papapumpkins/disa-myo-bionic-arm/20160616_183405.jpg

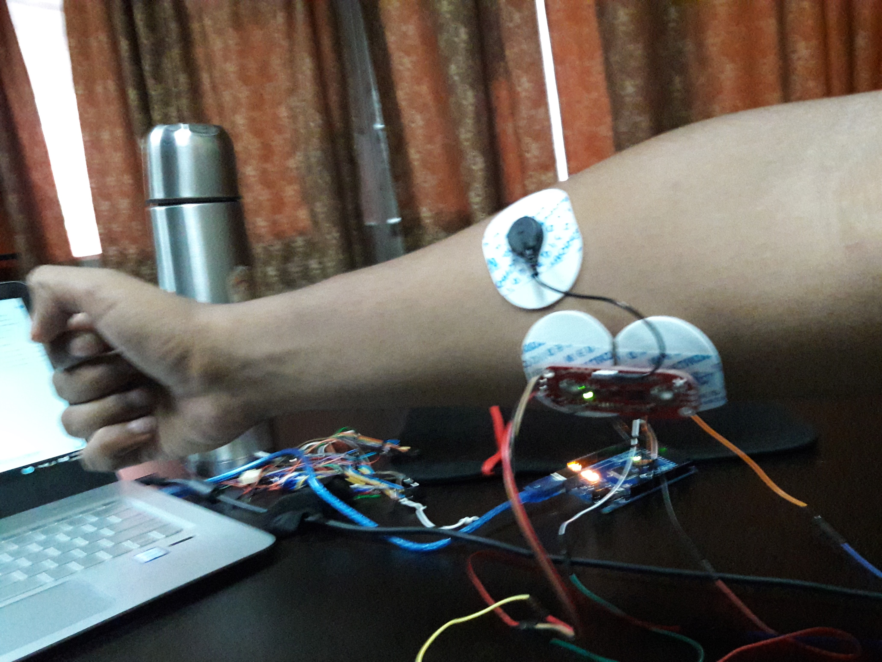
20160616_183405.jpg
