papapumpkins/disa-myo-bionic-arm/Servo CAD/futaba-servo/Renderings/Servo20111002-25129-4bc1xx.JPG

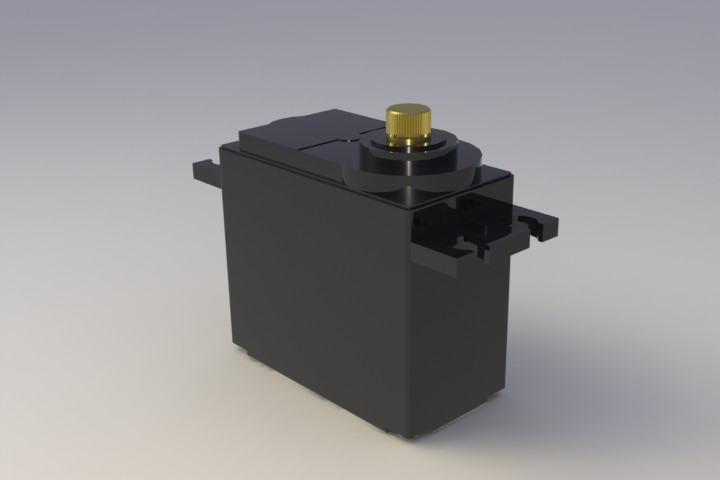
Servo CAD/futaba-servo/Renderings/Servo20111002-25129-4bc1xx.JPG
