papapumpkins/disa-myo-bionic-arm/Servo CAD/micro-servo-9g-1.snapshot.2/Renderings/MicroServo9g.png

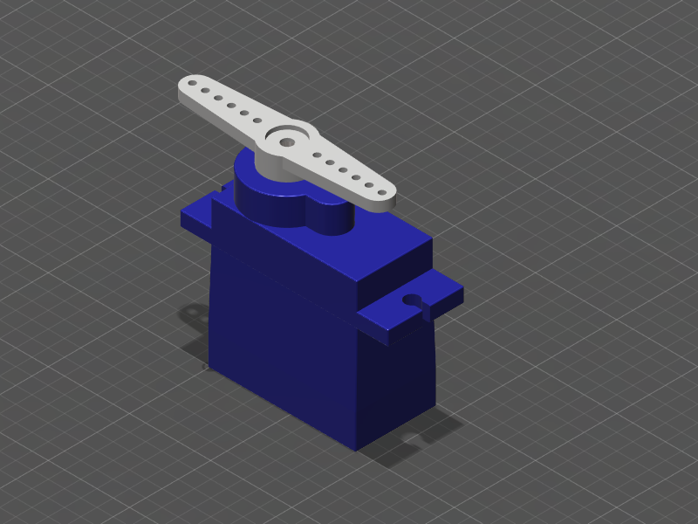
Servo CAD/micro-servo-9g-1.snapshot.2/Renderings/MicroServo9g.png
