papapumpkins/disa-myo-bionic-arm/Digits_Fingers_Base_20161126/Ring/Ring STL/Ring_Finger_assembly_1_Shaft_Piston_4.stl

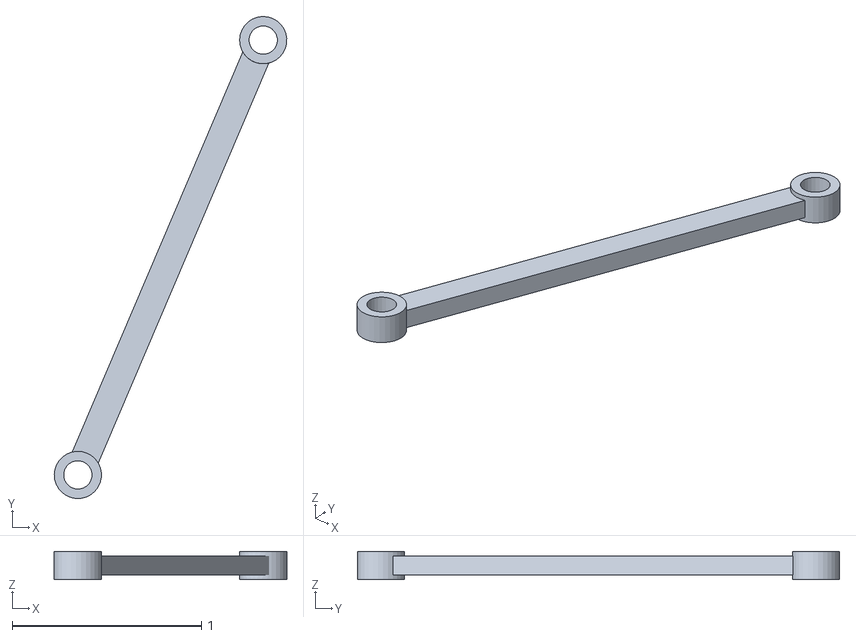
[picture p31: CAD file, 2018-10-29]
Digits_Fingers_Base_20161126/Ring/Ring STL/Ring_Finger_assembly_1_Shaft_Piston_4.stl
1.23 x 2.55 x 0.15
