papapumpkins/disa-myo-bionic-arm/Digits_Fingers_Base_20161126/ZIP STL 1/Pinky STL/Pinky_Assembly_01_Shaft_Piston_3.stl

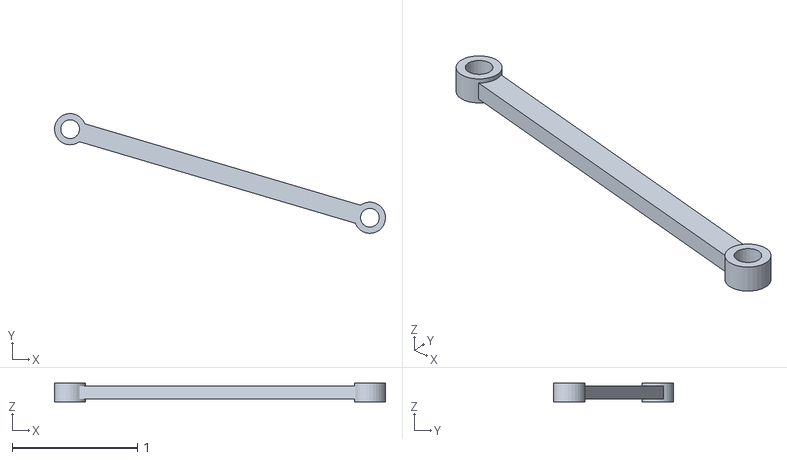
[picture p32: CAD file, 2018-10-29]
Digits_Fingers_Base_20161126/ZIP STL 1/Pinky STL/Pinky_Assembly_01_Shaft_Piston_3.stl
2.65 x 0.958 x 0.15
