papapumpkins/disa-myo-bionic-arm/Digits_Fingers_Base_20161126/ZIP STL 1/Thumb STL/Thumb_assembly_1.stl

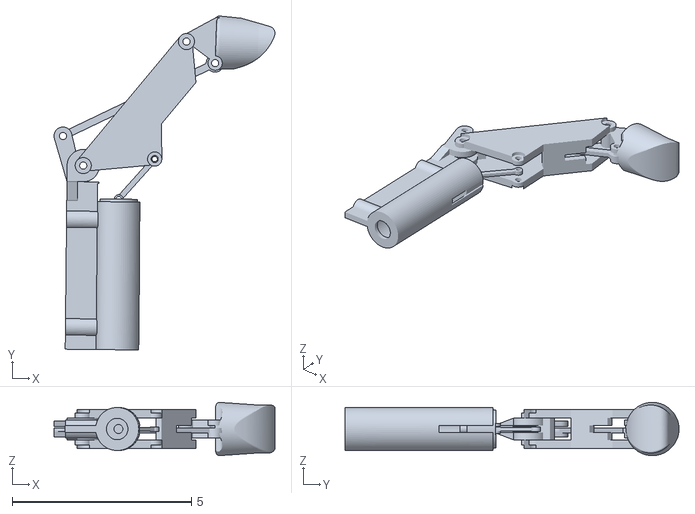
[picture p33: CAD file, 2018-10-29]
Digits_Fingers_Base_20161126/ZIP STL 1/Thumb STL/Thumb_assembly_1.stl
6.16 x 9.31 x 1.49
