papapumpkins/disa-myo-bionic-arm/Digits_Fingers_Base_20161126/ZIP STL 2/Index STL/Index_Finger_assembly_1_Shaft_Piston_2.stl

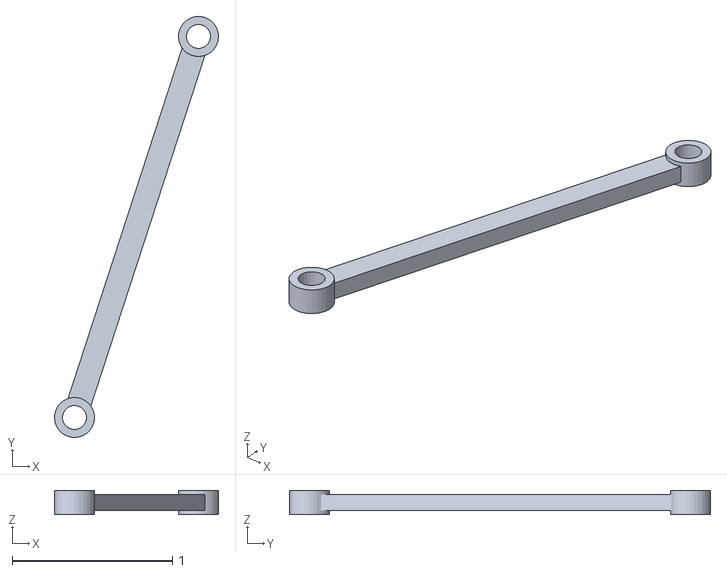
[picture p34: CAD file, 2018-10-29]
Digits_Fingers_Base_20161126/ZIP STL 2/Index STL/Index_Finger_assembly_1_Shaft_Piston_2.stl
1.02 x 2.63 x 0.15
