papapumpkins/disa-myo-bionic-arm/Digits_Fingers_Base_20161126/ZIP STL 2/Pinky STL/Pinky_ASSEMBLY_DONT_PRINT.stl

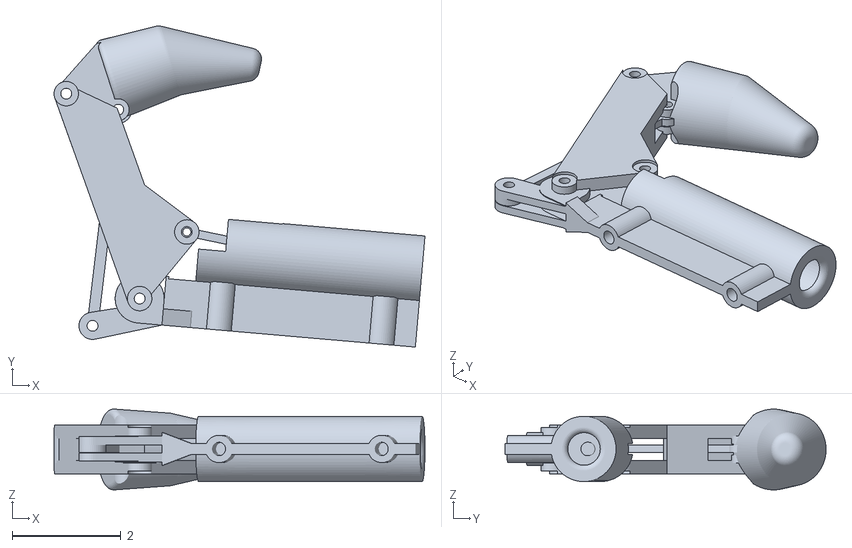
[picture p35: CAD file, 2018-10-29]
Digits_Fingers_Base_20161126/ZIP STL 2/Pinky STL/Pinky_ASSEMBLY_DONT_PRINT.stl
6.82 x 5.90 x 1.49
