papapumpkins/disa-myo-bionic-arm/Digits_Fingers_Base_20161029/Index+Middle/STL/Index_Finger_assembly_1_Base_Cylinder_11mm_5.stl

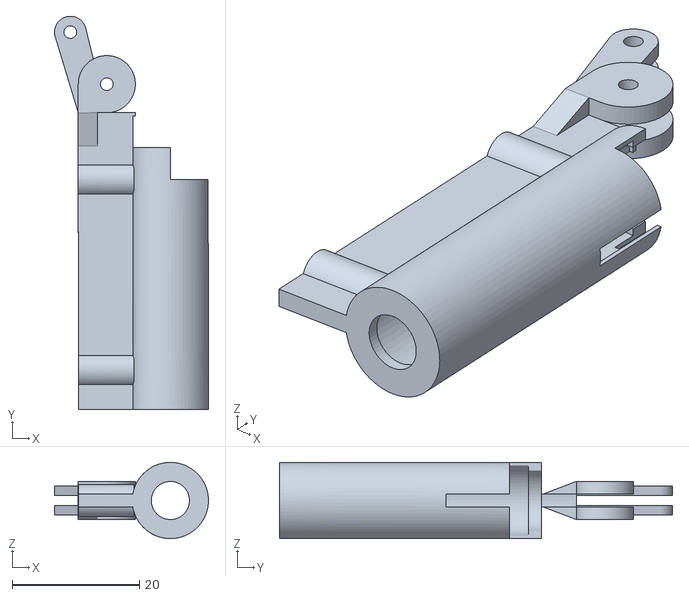
[picture p36: CAD file, 2018-10-29]
Digits_Fingers_Base_20161029/Index+Middle/STL/Index_Finger_assembly_1_Base_Cylinder_11mm_5.stl
24.2 x 61.9 x 12.0
