papapumpkins/disa-myo-bionic-arm/Digits_Fingers_Base_20161029/Pinky/Pinky_STL/Pinky_Assembly_01_Pinky_Upper_main_2_6.stl

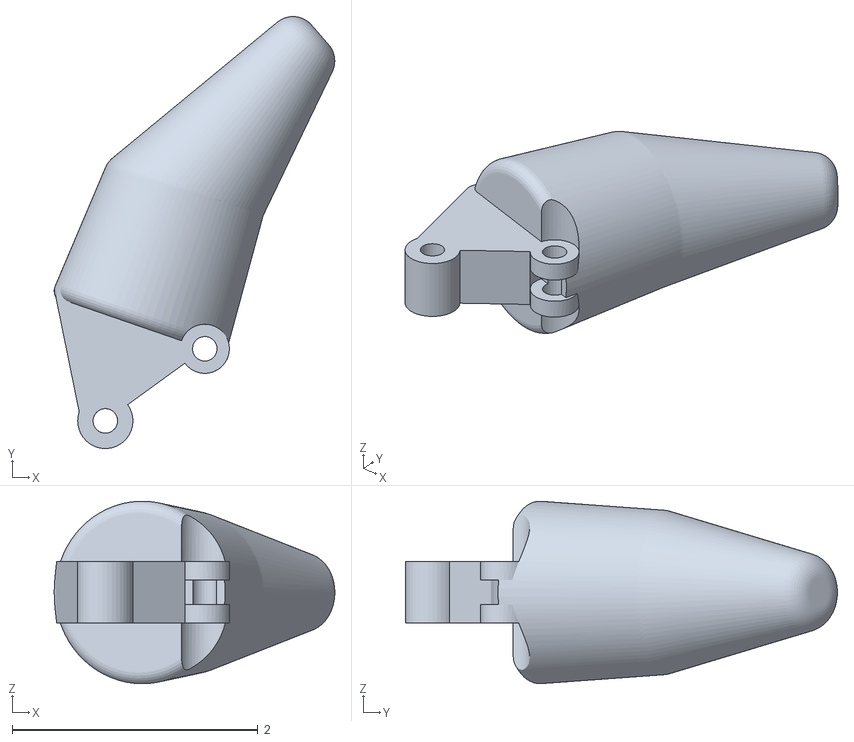
[picture p37: CAD file, 2018-10-29]
Digits_Fingers_Base_20161029/Pinky/Pinky_STL/Pinky_Assembly_01_Pinky_Upper_main_2_6.stl
2.28 x 3.52 x 1.49
