papapumpkins/disa-myo-bionic-arm/Digits_Fingers_Base_20161029/Ring/Ring STL/Ring_Finger_assembly_1_Ring_Upper_main_1_3.stl

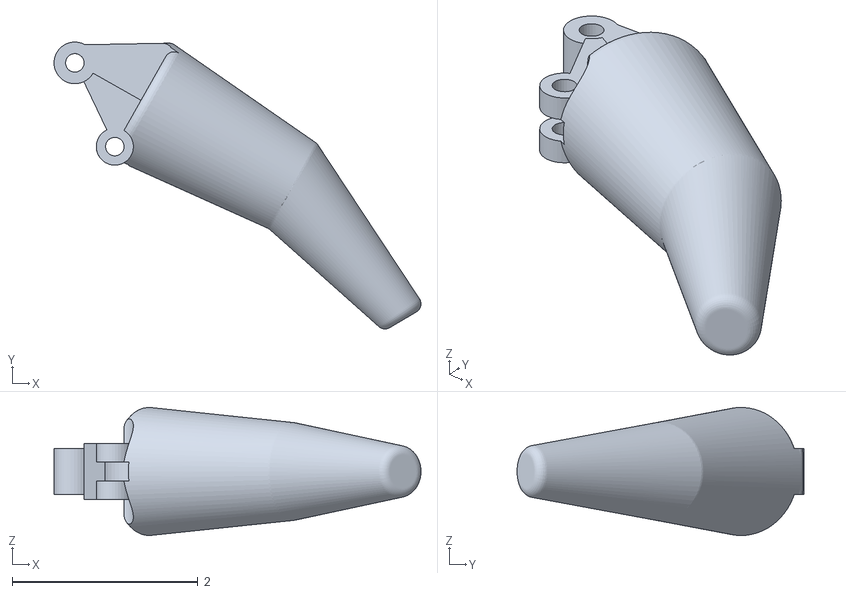
[picture p38: CAD file, 2018-10-29]
Digits_Fingers_Base_20161029/Ring/Ring STL/Ring_Finger_assembly_1_Ring_Upper_main_1_3.stl
3.96 x 3.09 x 1.38
