papapumpkins/disa-myo-bionic-arm/Digits_Fingers_Base_20161029/ZIP STL 1/Index STL/Index_Finger_assembly_1_Shaft_Piston_2.stl

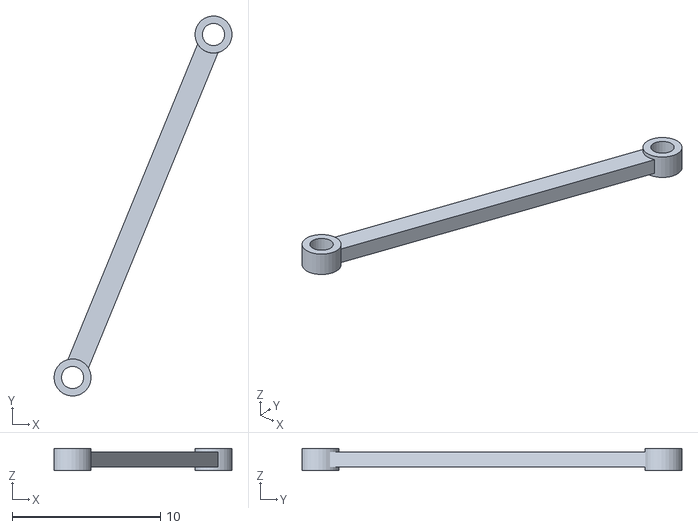
[picture p39: CAD file, 2018-10-29]
Digits_Fingers_Base_20161029/ZIP STL 1/Index STL/Index_Finger_assembly_1_Shaft_Piston_2.stl
12.0 x 25.6 x 1.50
