papapumpkins/disa-myo-bionic-arm/Digits_Fingers_Base_20161029/ZIP STL 1/Pinky STL/Pinky_Assembly_01.stl

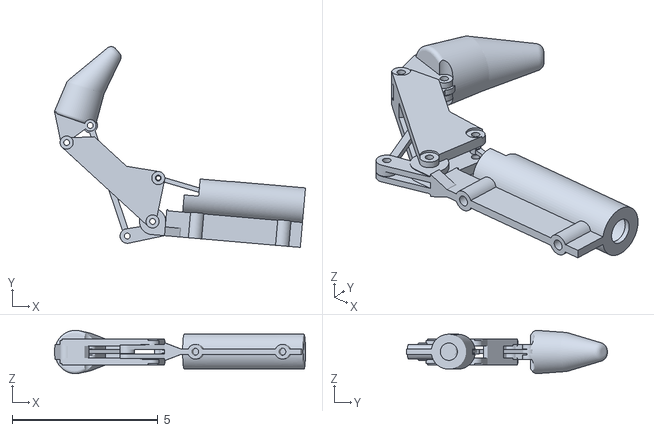
[picture p40: CAD file, 2018-10-29]
Digits_Fingers_Base_20161029/ZIP STL 1/Pinky STL/Pinky_Assembly_01.stl
8.61 x 6.89 x 1.49
