papapumpkins/disa-myo-bionic-arm/Digits_Fingers_Base_20161029/ZIP STL 2/Pinky STL/Pinky_Assembly_01_Base_Cylinder_Pinky_11mm_4.stl

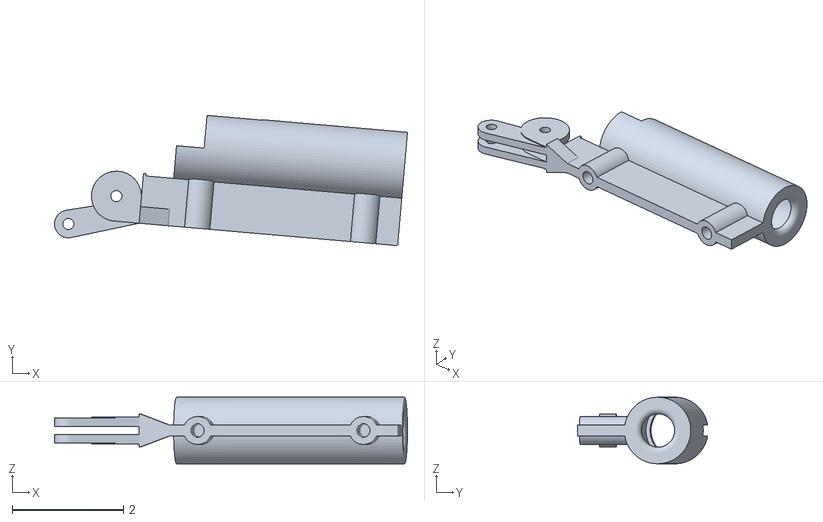
[picture p41: CAD file, 2018-10-29]
Digits_Fingers_Base_20161029/ZIP STL 2/Pinky STL/Pinky_Assembly_01_Base_Cylinder_Pinky_11mm_4.stl
6.36 x 2.35 x 1.20
