papapumpkins/disa-myo-bionic-arm/Digits_Fingers_Base_20161029/ZIP STL 2/Thumb STL/Thumb_assembly_1_Thumb_Restrain_Pin_1_3.stl

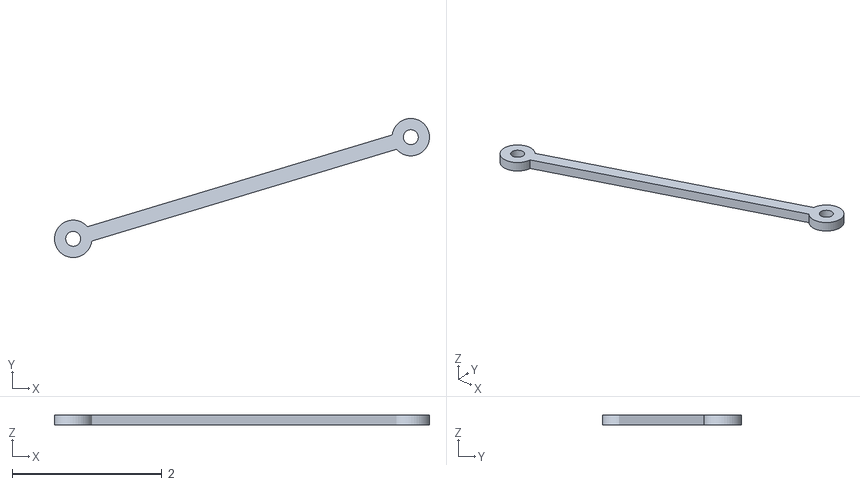
[picture p42: CAD file, 2018-10-29]
Digits_Fingers_Base_20161029/ZIP STL 2/Thumb STL/Thumb_assembly_1_Thumb_Restrain_Pin_1_3.stl
5.00 x 1.86 x 0.14
