papapumpkins/disa-myo-bionic-arm/Digits_Fingers_Base_20161126/Pinky/Pinky_STL/Pinky_Assembly_01_Pinky_Lower_main_1_5.stl

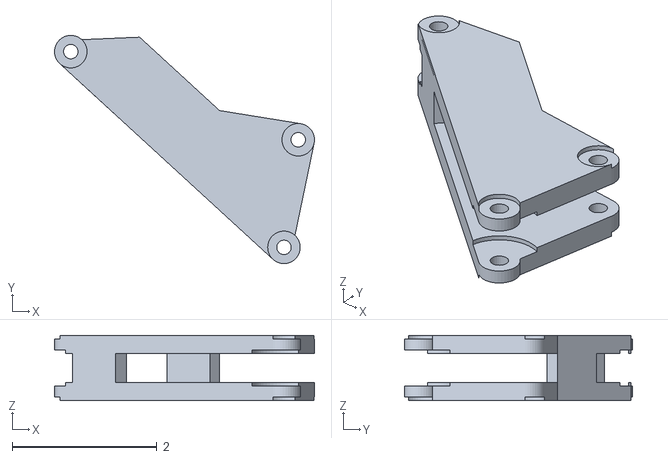
[picture p43: CAD file, 2018-10-29]
Digits_Fingers_Base_20161126/Pinky/Pinky_STL/Pinky_Assembly_01_Pinky_Lower_main_1_5.stl
3.59 x 3.15 x 0.9
