papapumpkins/disa-myo-bionic-arm/Digits_Fingers_Base_20161126/Thumb/Thumb_STL/Thumb_assembly_1_Thumb_Lower_main_1_1.stl

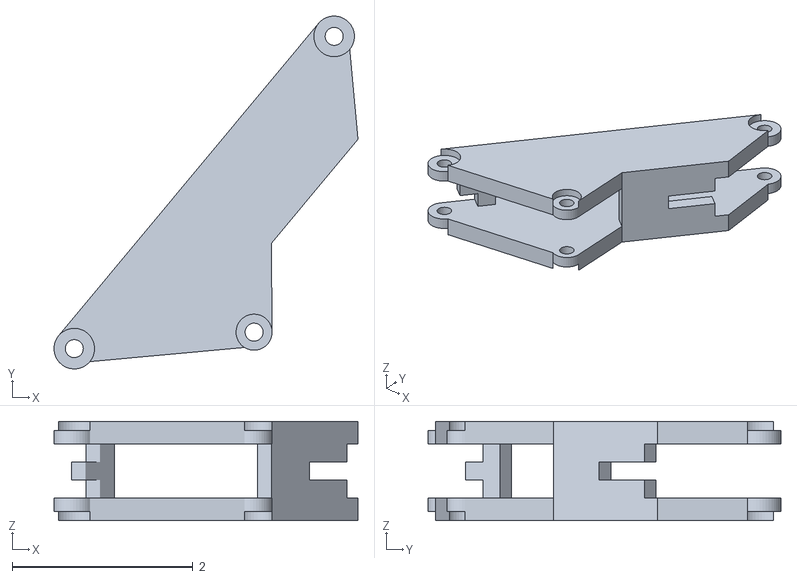
[picture p44: CAD file, 2018-10-29]
Digits_Fingers_Base_20161126/Thumb/Thumb_STL/Thumb_assembly_1_Thumb_Lower_main_1_1.stl
3.37 x 3.91 x 1.10
