papapumpkins/disa-myo-bionic-arm/Digits_Fingers_Base_20161126/ZIP STL 1/Index STL/Index_Finger_assembly_1_Index_Upper_main_1_4.stl

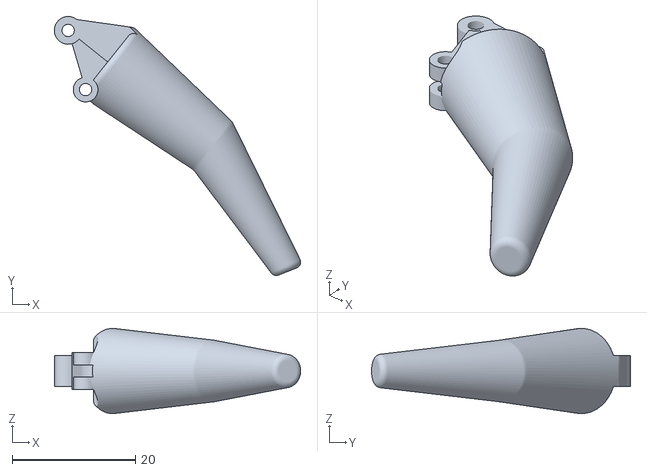
[picture p45: CAD file, 2018-10-29]
Digits_Fingers_Base_20161126/ZIP STL 1/Index STL/Index_Finger_assembly_1_Index_Upper_main_1_4.stl
39.9 x 42.0 x 13.8
