papapumpkins/disa-myo-bionic-arm/Digits_Fingers_Base_20161126/ZIP STL 1/Middle STL (Same as Index)/Index_Finger_assembly_1_Cylinder_10.5mm_6.stl

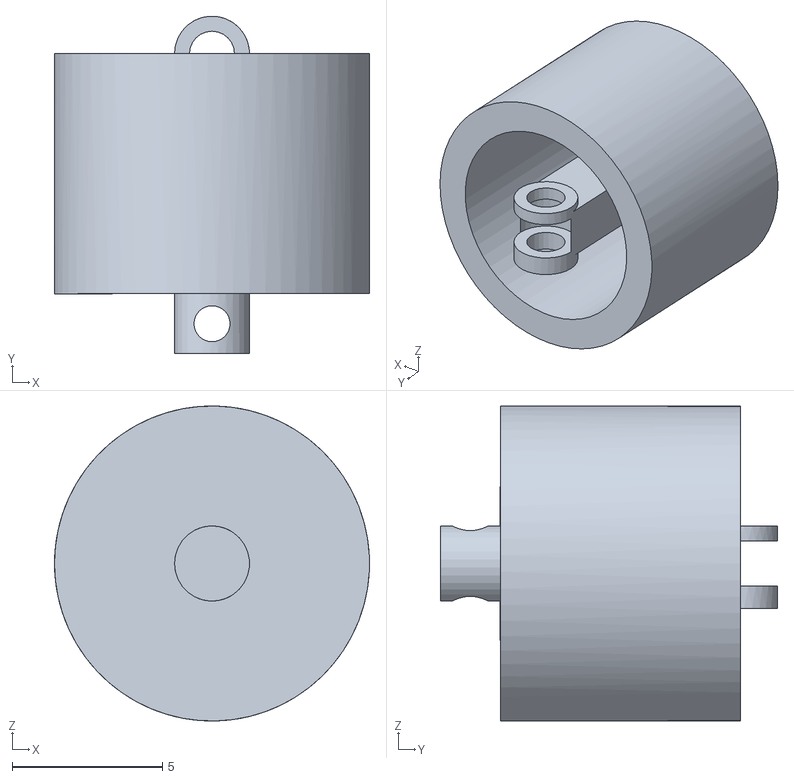
[picture p46: CAD file, 2018-10-29]
Digits_Fingers_Base_20161126/ZIP STL 1/Middle STL (Same as Index)/Index_Finger_assembly_1_Cylinder_10.5mm_6.stl
10.5 x 11.2 x 10.5
