papapumpkins/disa-myo-bionic-arm/Digits_Fingers_Base_20161126/ZIP STL 1/Ring STL/Ring_Finger_assembly_1_Restrain_Pin_1_2.stl

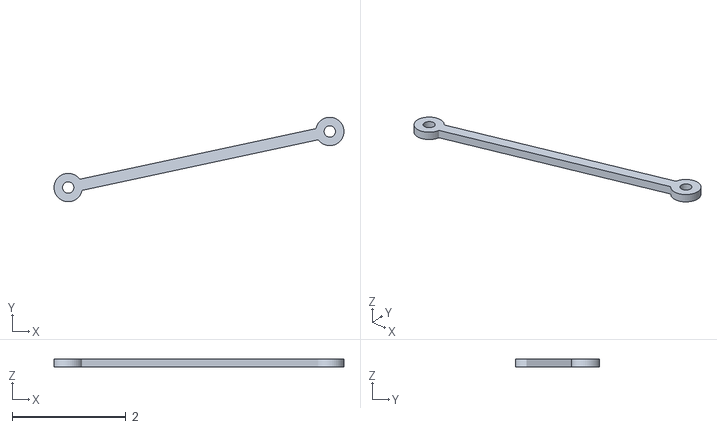
[picture p47: CAD file, 2018-10-29]
Digits_Fingers_Base_20161126/ZIP STL 1/Ring STL/Ring_Finger_assembly_1_Restrain_Pin_1_2.stl
5.10 x 1.49 x 0.14
