papapumpkins/disa-myo-bionic-arm/Digits_Fingers_Base_20161126/ZIP STL 2/Ring STL/Ring_Finger_assembly_1_Finger_Lower_main_1_1.stl

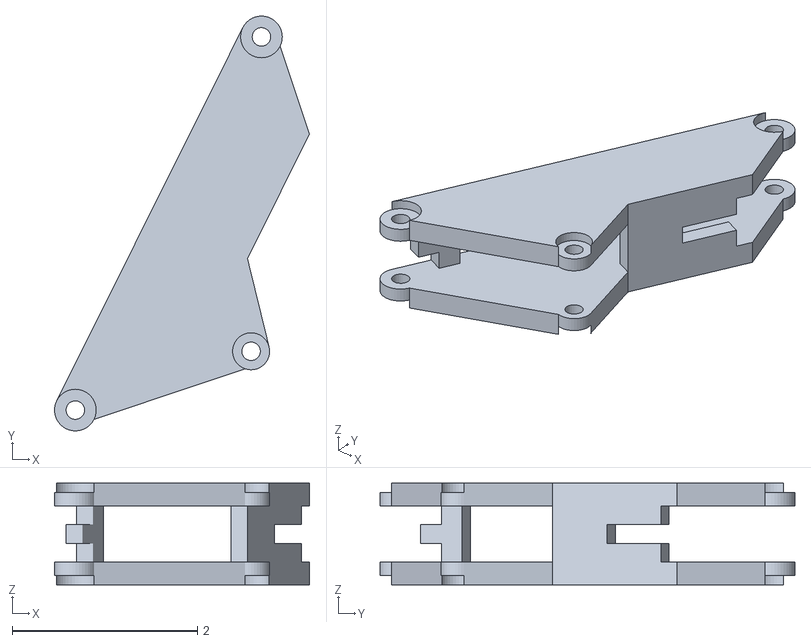
[picture p48: CAD file, 2018-10-29]
Digits_Fingers_Base_20161126/ZIP STL 2/Ring STL/Ring_Finger_assembly_1_Finger_Lower_main_1_1.stl
2.75 x 4.48 x 1.10
