papapumpkins/disa-myo-bionic-arm/Digits_Fingers_Base_20161029/Thumb/Thumb_STL/Thumb_assembly_1_ThumbNew_Base_Cylinder_11mm_4.stl

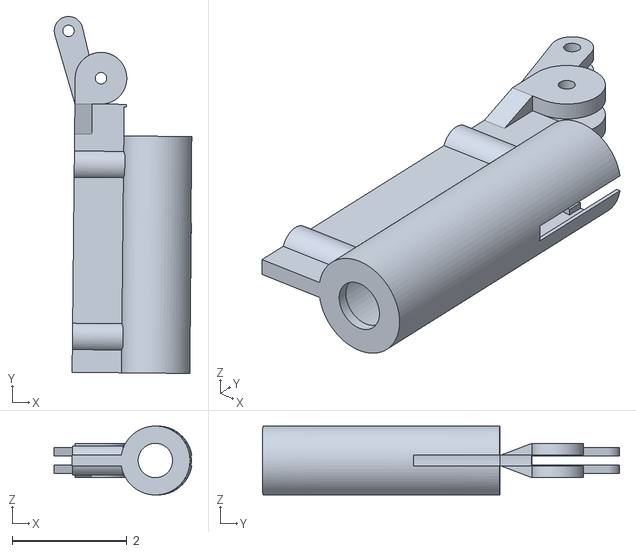
[picture p49: CAD file, 2018-10-29]
Digits_Fingers_Base_20161029/Thumb/Thumb_STL/Thumb_assembly_1_ThumbNew_Base_Cylinder_11mm_4.stl
2.40 x 6.22 x 1.20
