papapumpkins/disa-myo-bionic-arm/Digits_Fingers_Base_20161029/ZIP STL 2/Index STL/Index_Finger_assembly_1_Finger_Lower_main_1_1.stl

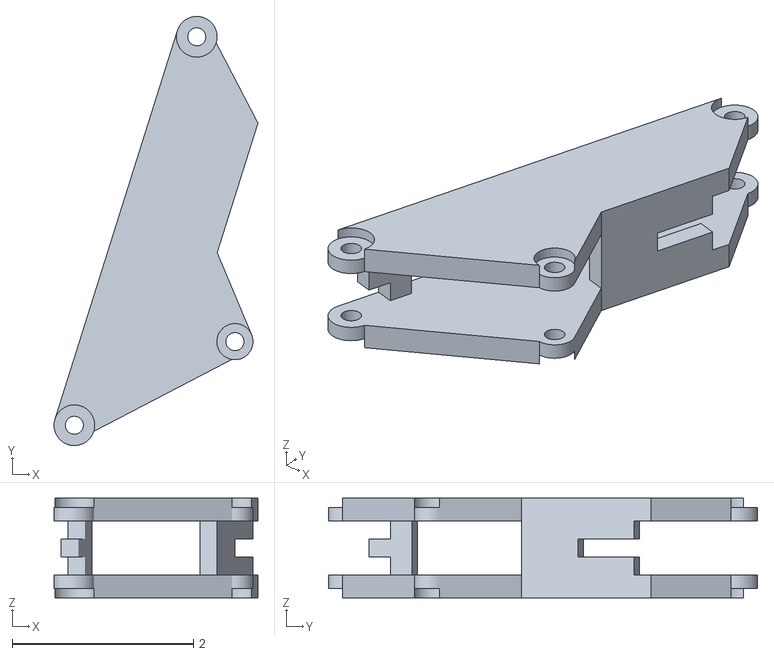
[picture p50: CAD file, 2018-10-29]
Digits_Fingers_Base_20161029/ZIP STL 2/Index STL/Index_Finger_assembly_1_Finger_Lower_main_1_1.stl
2.25 x 4.74 x 1.10
