papapumpkins/disa-myo-bionic-arm/Digits_Fingers_Base_20161029/ZIP STL 2/Middle STL (Same as Index)/Index_Finger_assembly_1_Base_Cylinder_11mm_5.stl

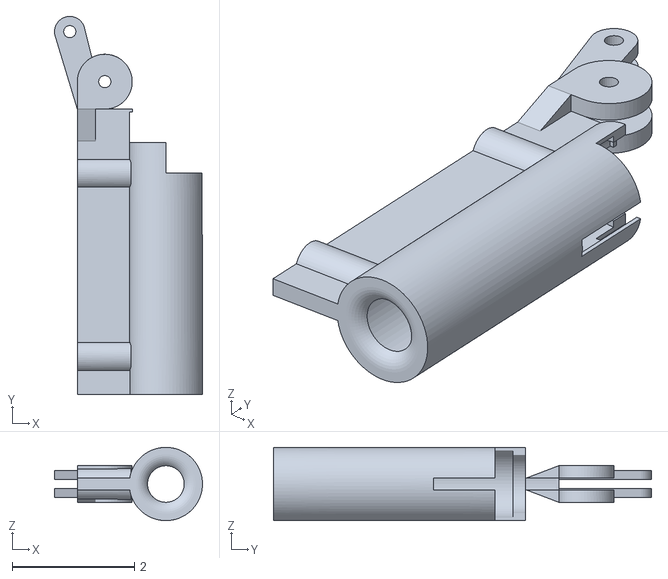
[picture p51: CAD file, 2018-10-29]
Digits_Fingers_Base_20161029/ZIP STL 2/Middle STL (Same as Index)/Index_Finger_assembly_1_Base_Cylinder_11mm_5.stl
2.42 x 6.19 x 1.20
