papapumpkins/disa-myo-bionic-arm/Digits_Fingers_Base_20161126/ZIP STL 1/Index STL/Index_Finger_ASSEMBLY_DONT_PRINT.stl

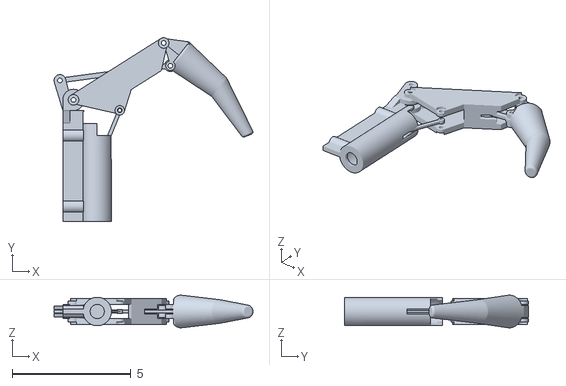
[picture p53: CAD file, 2018-10-29]
Digits_Fingers_Base_20161126/ZIP STL 1/Index STL/Index_Finger_ASSEMBLY_DONT_PRINT.stl
8.40 x 7.75 x 1.38
