papapumpkins/disa-myo-bionic-arm/Digits_Fingers_Base_20161126/ZIP STL 2/Middle STL (Same as Index)/Index_Finger_ASSEMBLY_DONT_PRINT.stl

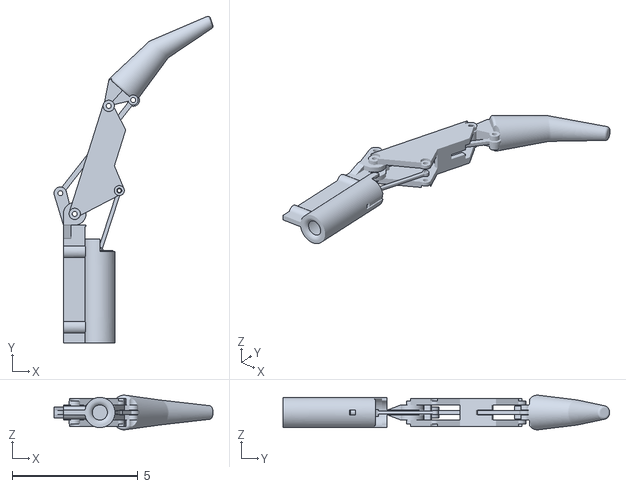
[picture p54: CAD file, 2018-10-29]
Digits_Fingers_Base_20161126/ZIP STL 2/Middle STL (Same as Index)/Index_Finger_ASSEMBLY_DONT_PRINT.stl
6.32 x 13.0 x 1.38
