papapumpkins/disa-myo-bionic-arm/Digits_Fingers_Base_20161126/ZIP STL 2/Pinky STL/Pinky_Assembly_01_Pinky_Lower_main_1_5.stl

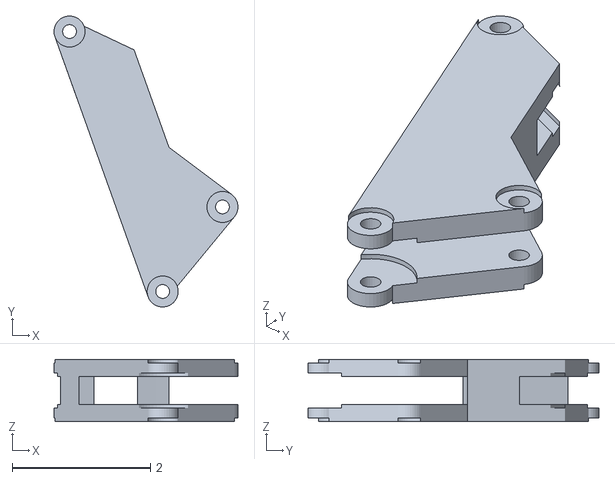
[picture p55: CAD file, 2018-10-29]
Digits_Fingers_Base_20161126/ZIP STL 2/Pinky STL/Pinky_Assembly_01_Pinky_Lower_main_1_5.stl
2.67 x 4.21 x 0.9
