papapumpkins/disa-myo-bionic-arm/Digits_Fingers_Base_20161126/ZIP STL 2/Ring STL/Ring_Finger_ASSEMBLY_DONT_PRINT.stl

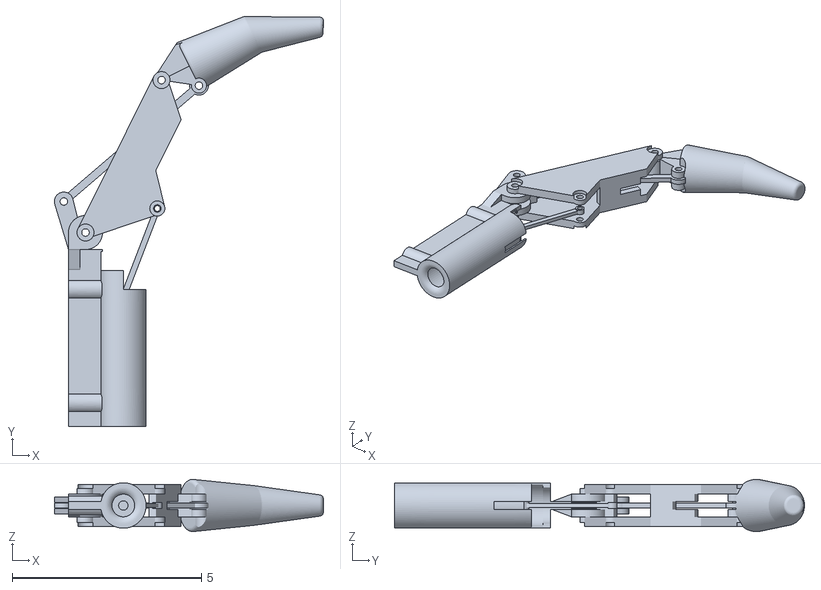
[picture p56: CAD file, 2018-10-29]
Digits_Fingers_Base_20161126/ZIP STL 2/Ring STL/Ring_Finger_ASSEMBLY_DONT_PRINT.stl
7.11 x 10.8 x 1.38
