papapumpkins/disa-myo-bionic-arm/Digits_Fingers_Base_20161029/ZIP STL 2/Pinky STL/Pinky_Assembly_01_Shaft_Piston_3.stl

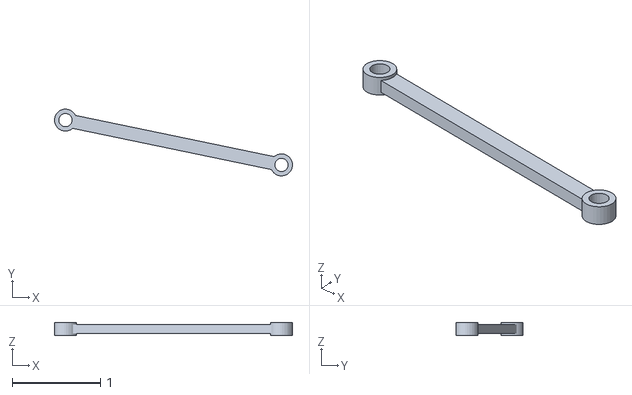
[picture p57: CAD file, 2018-10-29]
Digits_Fingers_Base_20161029/ZIP STL 2/Pinky STL/Pinky_Assembly_01_Shaft_Piston_3.stl
2.70 x 0.758 x 0.15
