papapumpkins/disa-myo-bionic-arm/Digits_Fingers_Base_20161029/ZIP STL 2/Ring STL/Ring_Finger_assembly_1_Shaft_Piston_4.stl

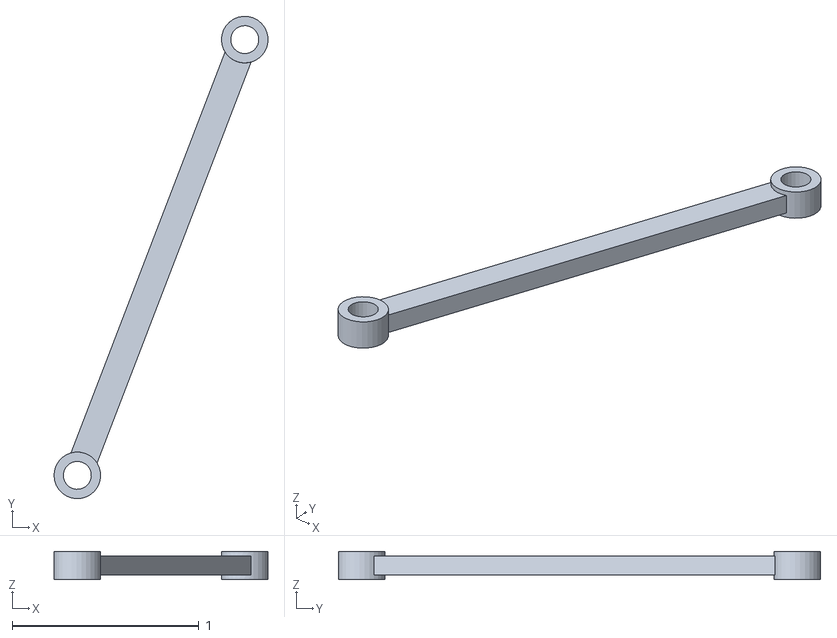
[picture p58: CAD file, 2018-10-29]
Digits_Fingers_Base_20161029/ZIP STL 2/Ring STL/Ring_Finger_assembly_1_Shaft_Piston_4.stl
1.15 x 2.58 x 0.15
