papapumpkins/disa-myo-bionic-arm/Digits_Fingers_Base_20161126/ZIP STL 2/Ring STL/Ring_Finger_assembly_1_Restrain_Pin_1_2.stl

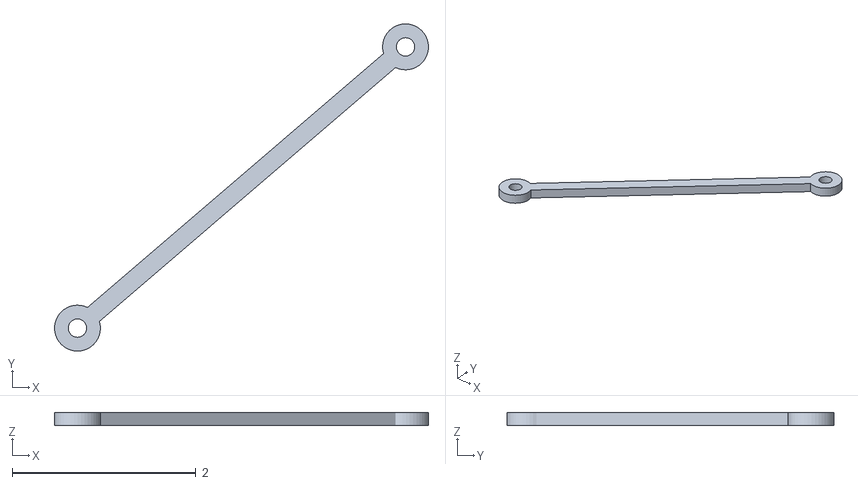
[picture p59: CAD file, 2018-10-29]
Digits_Fingers_Base_20161126/ZIP STL 2/Ring STL/Ring_Finger_assembly_1_Restrain_Pin_1_2.stl
4.07 x 3.56 x 0.14
