papapumpkins/disa-myo-bionic-arm/Digits_Fingers_Base_20161029/ZIP STL 2/Pinky STL/Pinky_Assembly_01_Restrain_Pin_Pinky_1_2.stl

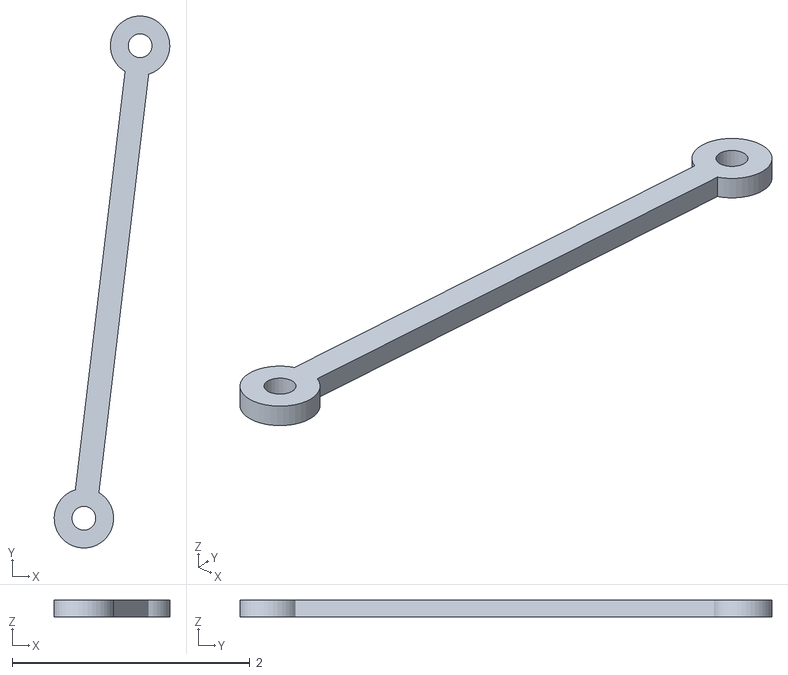
[picture p60: CAD file, 2018-10-29]
Digits_Fingers_Base_20161029/ZIP STL 2/Pinky STL/Pinky_Assembly_01_Restrain_Pin_Pinky_1_2.stl
0.972 x 4.47 x 0.14
