papapumpkins/disa-myo-bionic-arm/Digits_Fingers_Base_20161029/ZIP STL 2/Thumb STL/Thumb_ASSEMBLY_DONT_PRINT.stl

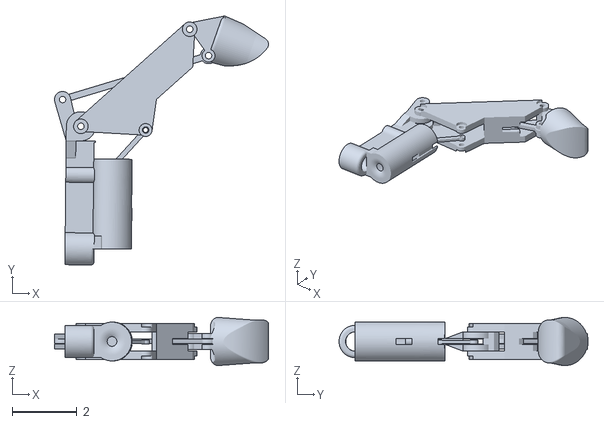
[picture p61: CAD file, 2018-10-29]
Digits_Fingers_Base_20161029/ZIP STL 2/Thumb STL/Thumb_ASSEMBLY_DONT_PRINT.stl
6.60 x 7.68 x 1.48
