papapumpkins/disa-myo-bionic-arm/Digits_Fingers_Base_20161126/ZIP STL 2/Thumb STL/Thumb_assembly_1_Thumb_Lower_main_1_1.stl

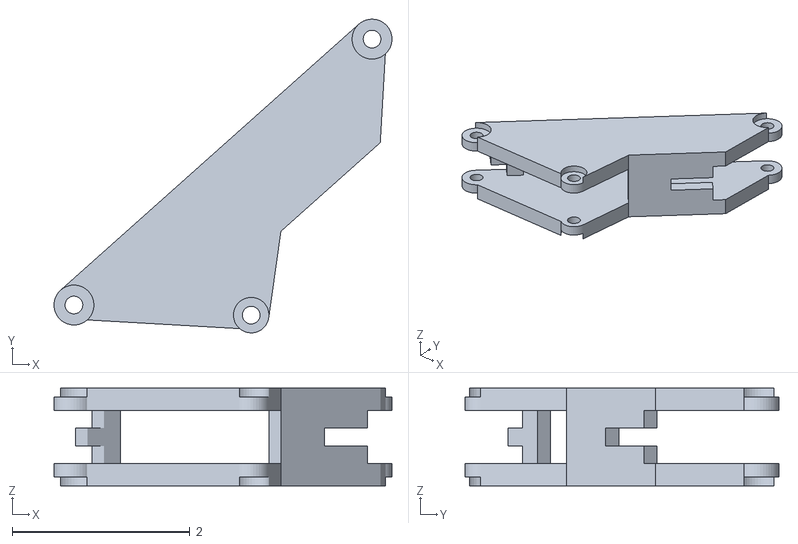
[picture p62: CAD file, 2018-10-29]
Digits_Fingers_Base_20161126/ZIP STL 2/Thumb STL/Thumb_assembly_1_Thumb_Lower_main_1_1.stl
3.81 x 3.53 x 1.10
